rakeshratheeshan/class-d-audio-amplifier/Breadboard_impementation_and_Observation/Driver+filter.jpeg

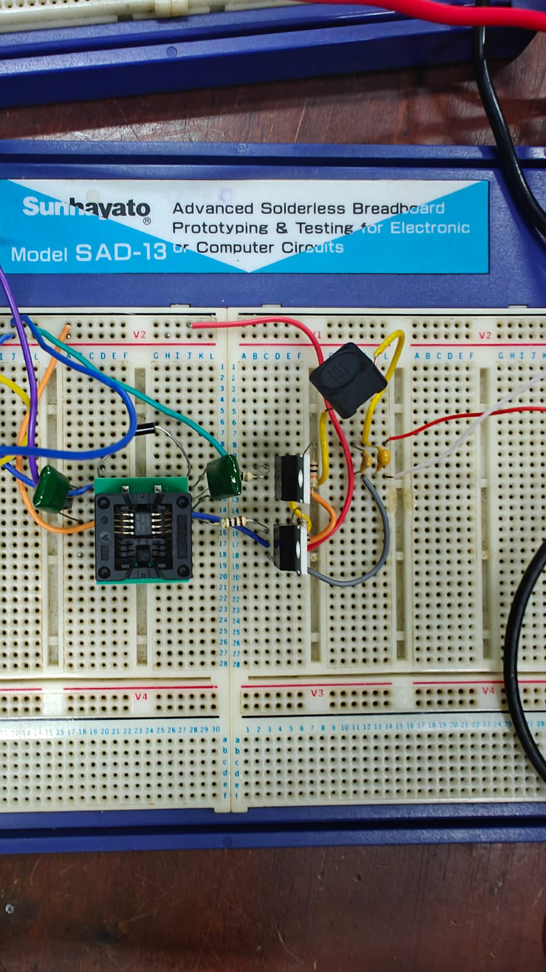
Breadboard_impementation_and_Observation/Driver+filter.jpeg
