rakeshratheeshan/class-d-audio-amplifier/Breadboard_impementation_and_Observation/driver_out.jpeg

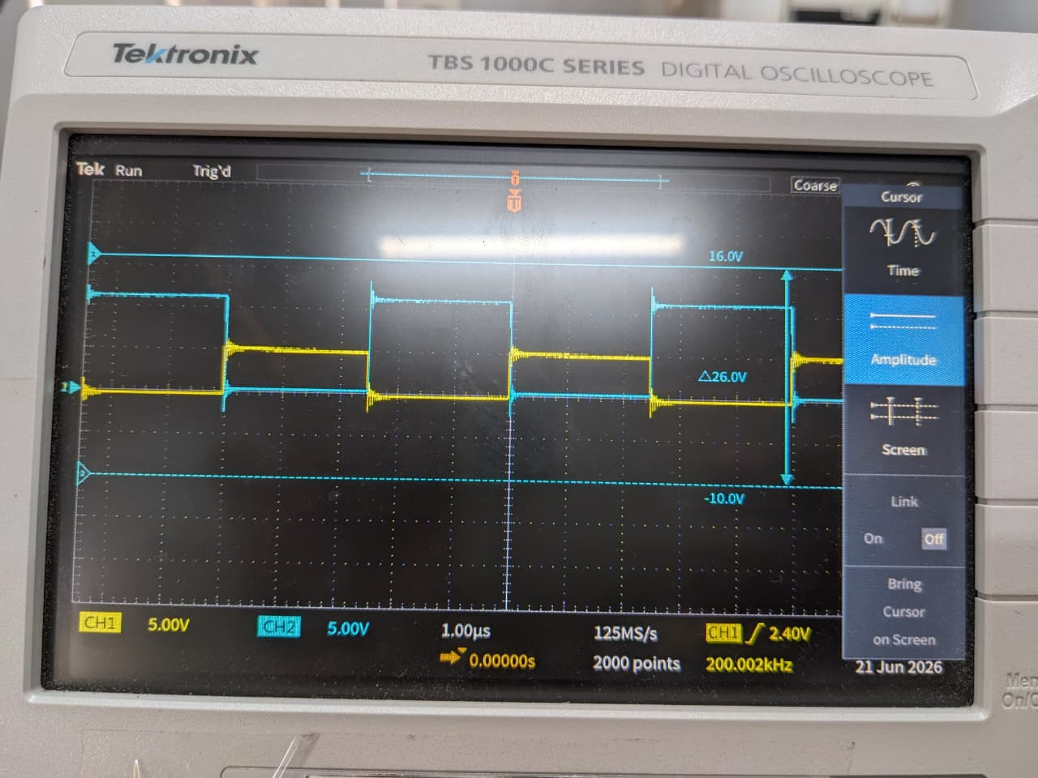
Breadboard_impementation_and_Observation/driver_out.jpeg
