rakeshratheeshan/class-d-audio-amplifier/Breadboard_impementation_and_Observation/triangular.jpeg

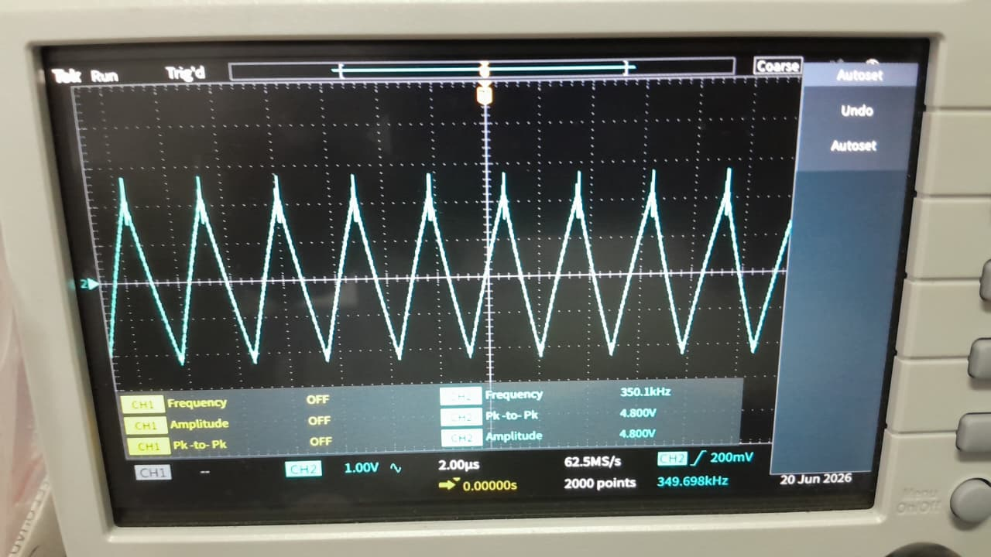
Breadboard_impementation_and_Observation/triangular.jpeg
