rakeshratheeshan/class-d-audio-amplifier/LTSpice Simulations/classD_with_ir2104.asc

C1: cap; 330p
C2: cap; 47p
C3: cap; 100n
C4: cap; 1.2µ
C5: cap; 400n
D1: diode; MUR860G
L1: ind; 70µ; Rser=.1
L2: ind; 60µ; Rser=.1
M1: nmos; IRF530
M2: nmos; IRF530
R1: res; 10k
R2: res; 10k
R3: res; 3.9k
R4: res; 35k
R5: res; 100k
R6: res; 1k
R7: res; 10Meg
R8: res; 8
U1: IR2104
U2: AD8065
U3: AD8065
U4: LM311
V1: voltage; 5
V2: voltage; SINE(0 2.9 20k)
V3: voltage; PULSE(-3 3 0 {Tr} {Tf} 0 {T})
V4: voltage; 5
V5: voltage; 12
Named nets: PWM, 0, Square, Triangle, v+, v-, Tri, sig, VCC, vs, V_out, out
.tran 1m
Astable Multivibrator
Integrator Circuit
.tran 1000u
.param f=300k
.param Tr={1/(2*f)}
.param Tf={1/(2*f)}
.param T={1/f}
* MUR860G SPICE Model
* Ultrafast Recovery Rectifier: 600V, 8A
.MODEL MUR860G D (
+ IS=1.03e-7 
+ RS=0.038 
+ N=1.8 
+ TT=4.3e-8 
+ CJO=2.2e-10 
+ VJ=0.7 
+ M=0.45 
+ BV=600 
+ IBV=1e-5 
+ EG=1.11 
+ XTI=3 
+ T_MEAS=25)
