rakeshratheeshan/class-d-audio-amplifier/LTSpice Simulations/filter/filter_comparison.asc

C1: cap; {C}
C2: cap; {C}
C3: cap; 0.56µ
C4: cap; 630n
C5: cap; 1.56µ
C6: cap; 330n
C7: cap; 0.63µ
C8: cap; 1m
C9: cap; 1.2µ
C10: cap; 400n
C11: cap; 100µ
C12: cap; 1.56µ
C13: cap; 330n
C14: cap; 220n
L1: ind; 72µ
L2: ind; 100µ; Rser=1m
L3: ind; 100µ; Rser=1m
L4: ind; 68µ; Rser=1m
L5: ind; 100µ; Rser=1m
L6: ind; 70µ; Rser=.1
L7: ind; 60µ; Rser=.1
L8: ind; 100µ; Rser=1m
L9: ind; 68µ; Rser=1m
L10: ind; 68µ; Rser=1m
R1: res; {R}
R2: res; {R}
R3: res; 56k
R4: res; 33k
R5: res; 0.5
R6: res; {R1}
R7: res; {R1}
R8: res; {R1}
R9: res; 8
R10: res; 8
R11: res; 5.6
R12: res; {R1}
R13: res; 4
U1: opamp2; NE5532
V2: voltage; 15
V3: voltage; -15
V4: voltage; SINE(0 1 1k); AC 1
Named nets: 0, Vout, Vin, Vpos, Vneg, Vout_P1, Vout_P2, Vout_P_zobel, Vout_P_mid, old, Vout_P3
.param R=6200
.param C=1nF
.tran 100m
.ac dec 100 1k 100k
.lib NE5532.sub
2nd order active low pass butterworth filter
2nd order butterworth passive LPF
.param R1 = 8
fc = 1/2*pi*sqrt(LC)
fc = 25.064khz
Speaker
2nd order butterwoth for the Mid eval
4th order under 8 ohm load
4th order considering variable load conditions
