rakeshratheeshan/class-d-audio-amplifier/LTSpice Simulations/gate-driver/Class_D4_with_UCC27517.asc

C1: cap; 330p
C2: cap; 47p
C3: cap; 220p
C4: cap; 10µf
C8: cap; 1.2µ
C9: cap; 400n
C10: cap; 1m
C11: cap; 0.63µ
C12: cap; 220p
C14: cap; 100n
D1: diode; MUR860G
D2: diode; SS3P5
D3: diode; SS3P5
L1: ind; 70µ; Rser=.1
L2: ind; 60µ; Rser=.1
L3: ind; 100µ; Rser=1m
M3: nmos; IRF530
M4: nmos; IRF530
R1: res; 2.2k
R2: res; 2.2k
R7: res; 10k
R8: res; 10k
R9: res; 3.9k
R10: res; 35k
R11: res; 100k
R12: res; 1k
R13: res; 10Meg
R24: res; 8
R30: res; 8
U1: AD8065
U2: AD8065
U3: UCC27517_TRANS
U7: UCC27517_TRANS
U8: UCC27517_TRANS
U9: LM311
V1: voltage; 5
V2: voltage; 12
V3: voltage; SINE(0 2.8 20k)
V5: voltage; PULSE(-3 3 0 {Tr} {Tf} 0 {T})
V6: voltage; 12
V8: voltage; 5
Named nets: out, 0, Vout_P, V_out, 12, PWMA, PWMB, PWM, vs, Square, Triangle, v+, v-, sig, Tri
2nd order butterworth passive LPF
.param R1 = 8
fc = 1/2*pi*sqrt(LC)
fc = 25.064khz
Speaker
.tran 1m
Astable Multivibrator
Integrator Circuit
.tran 1000u
.param f=300k
.param Tr={1/(2*f)}
.param Tf={1/(2*f)}
.param T={1/f}
* MUR860G SPICE Model
* Ultrafast Recovery Rectifier: 600V, 8A
.MODEL MUR860G D (
+ IS=1.03e-7 
+ RS=0.038 
+ N=1.8 
+ TT=4.3e-8 
+ CJO=2.2e-10 
+ VJ=0.7 
+ M=0.45 
+ BV=600 
+ IBV=1e-5 
+ EG=1.11 
+ XTI=3 
+ T_MEAS=25)
